madworx/tms5220-atmega/software/lpc10.h

const unsigned char lpc10[] = {
0x80,0xd2,0x11,0xdc,0x54,0x4d,0x52,0x4a,0xb2,0x11,0x53,0xdf,0x98,0x2d,0x2d,0x4e,0x8d,0x63,0x62,0xa7,0x34,0x69,0x76,0xb3,0x72,0x1a,0xd2,0x64,0xb0,0x2c,0xd2,0x59,0x48,0xb3,0x81,0xb6,0x4a,0x67,0x25,0x29,0x86,0xc3,0x3d,0xa6,0xb4,0x64,0x38,0x16,0x0f,0xab,0x1d,0x80,0x35,0xb7,0x1d,0xb0,0xe7,0x8e,0x03,0x76,0xbf,0x71,0xc0,0x1e,0xd7,0x0e,0x58,0x65,0xab,0x48,0x5d,0x31,0x5b,0x75,0xec,0x94,0x15,0x4e,0x35,0x6d,0x54,0x42,0x5a,0x04,0x4e,0x17,0x2b,0x0d,0x62,0x14,0xd2,0x9d,0xec,0x38,0xc8,0x4e,0x65,0x79,0x9a,0x6a,0xa7,0x70,0x93,0xe5,0xe9,0x8e,0x95,0xce,0x4c,0x8e,0x35,0xbb,0x4e,0xc6,0x54,0x8e,0x62,0x6e,0xcf,0x00,0x3f,0xba,0x39,0xe0,0x6a,0xcb,0xb2,0x77,0x9b,0xe1,0xa6,0x94,0x8c,0x9b,0x58,0x58,0x9a,0x26,0x56,0xbe,0xcc,0xed,0xce,0x5a,0xc7,0x04,0x66,0x7a,0x19,0x44,0x1b,0x17,0xda,0x65,0x5a,0x58,0x75,0x42,0xe4,0xbb,0xd8,0x72,0xce,0x09,0x71,0x68,0x14,0x6b,0xd1,0x38,0xc5,0xb1,0x91,0xaf,0x65,0x92,0x90,0xc4,0xca,0xf2,0x1e,0x71,0x42,0x9a,0x1a,0xe9,0x49,0x36,0x0a,0x69,0x99,0xa4,0x4b,0x39,0x55,0xed,0xb9,0x61,0xb6,0xf6,0x12,0x24,0xa4,0x24,0x3e,0x51,0xdd,0xc8,0x35,0x92,0x67,0x9a,0xa5,0x45,0xd7,0x2c,0x91,0xab,0x92,0x04,0xd0,0xd1,0x7c,0xb8,0x6a,0xd8,0x0e,0xf1,0x08,0x5a,0x2e,0xed,0x78,0x14,0x35,0x98,0x9a,0x8e,0xad,0x52,0x54,0x27,0x2a,0xb2,0x0a,0x5d,0x11,0x05,0x65,0xf9,0xb2,0x72,0x79,0x10,0x94,0x1d,0xcb,0x3a,0xe4,0x49,0x93,0x5b,0x8f,0xa3,0x91,0xb6,0xaa,0x8a,0xd5,0x2e,0x56,0xdc,0xb3,0x3a,0x4d,0xd9,0x5c,0x61,0xf5,0x16,0x3a,0x61,0xf9,0x04,0x35,0x5a,0xe8,0x84,0x9c,0x15,0x54,0xeb,0x29,0x55,0x56,0x5a,0x5c,0xb4,0xb7,0x84,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
